Oldfusiondesigns/OFD_Flycore_Straight_Talon/Images/Capture.PNG

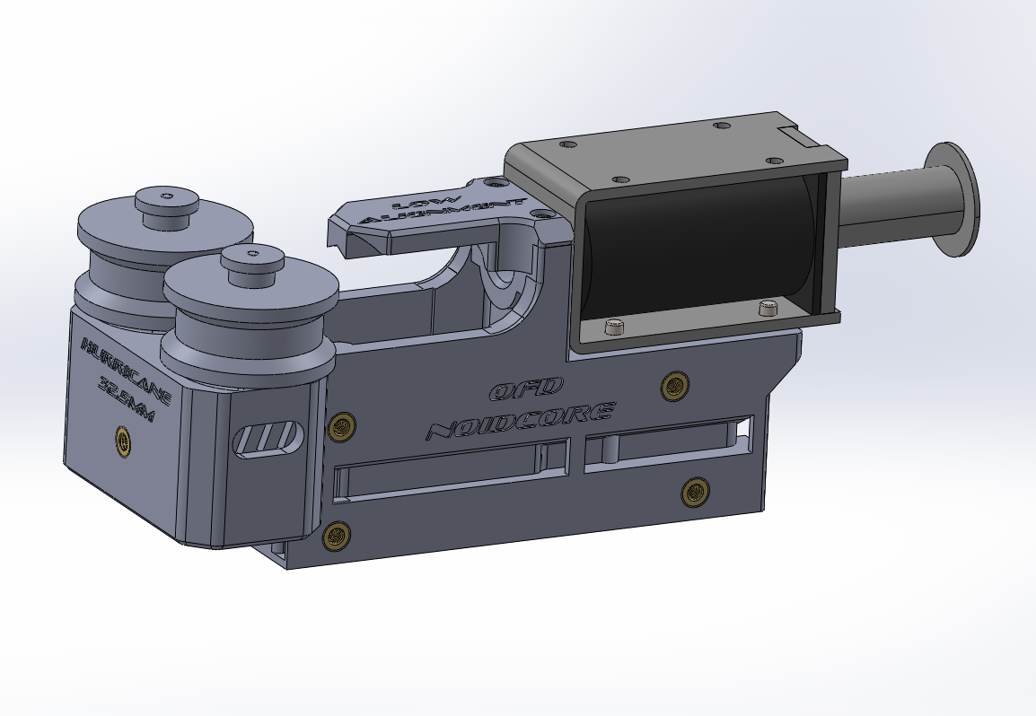
Images/Capture.PNG
