Oldfusiondesigns/OFD_Flycore_Straight_Talon/Images/heatsets.jpg

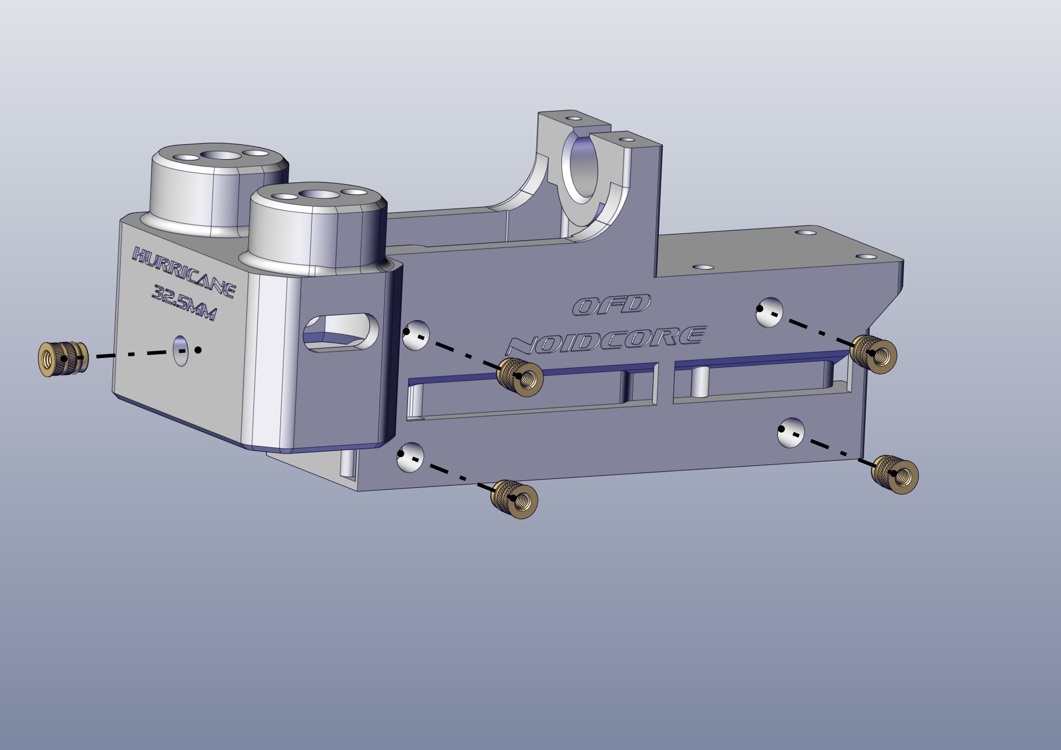
Images/heatsets.jpg
