Oldfusiondesigns/OFD_Flycore_Straight_Talon/Flycore Straight Talon/STLs/Flywheel_Spacers/OFD_Flywheel_Spacer_3.5mm_V1.STL

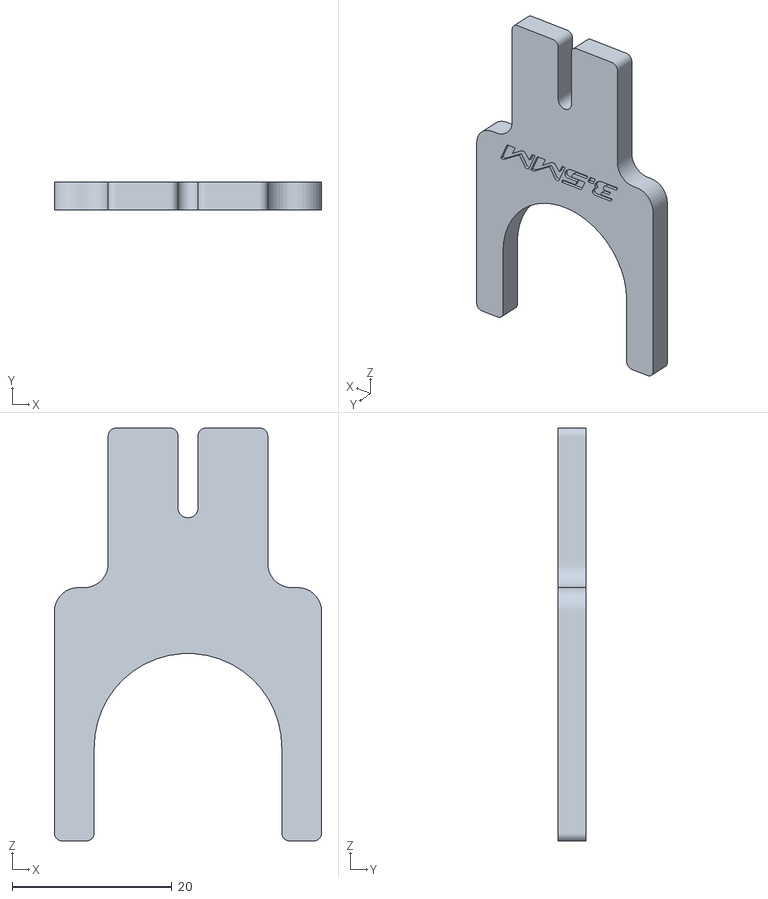
[picture p27: CAD file, 2022-10-01]
Flycore Straight Talon/STLs/Flywheel_Spacers/OFD_Flywheel_Spacer_3.5mm_V1.STL
33.5 x 3.50 x 51.8
