Oldfusiondesigns/OFD_Flycore_Straight_Talon/Flycore Straight Talon/STEPs/Pusher_Wheel_Plus_.4_V1.STEP

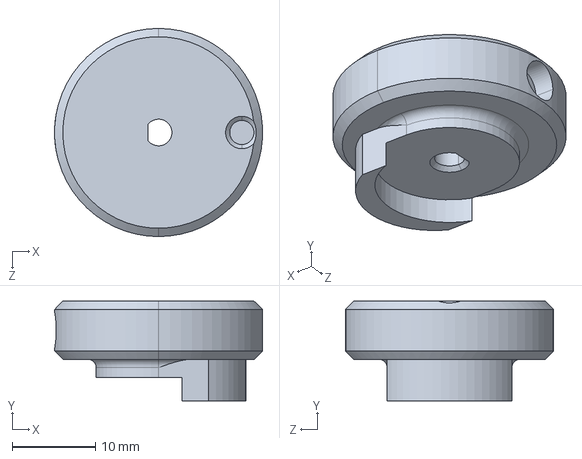
[picture p28: CAD file, 2022-10-01]
Flycore Straight Talon/STEPs/Pusher_Wheel_Plus_.4_V1.STEP
25.0 x 12.0 x 25.0 mm
