Oldfusiondesigns/OFD_Flycore_Straight_Talon/Flycore Straight Talon/STLs/Flywheel_Spacers/OFD_Flywheel_Spacer_2mm_V1.STL

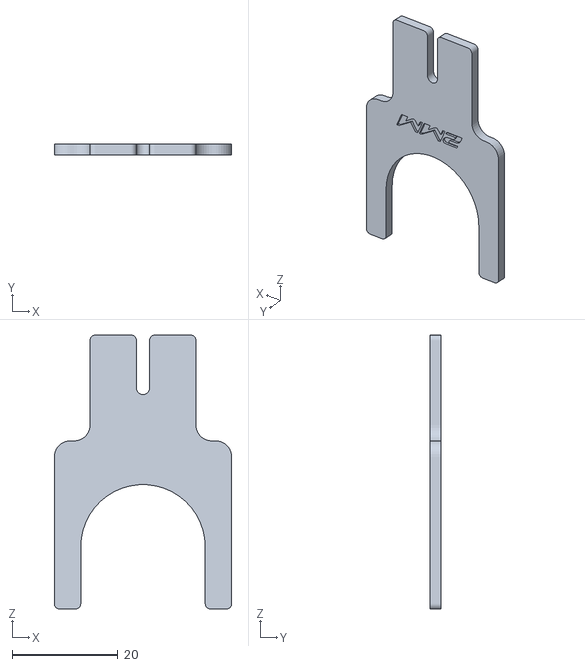
[picture p29: CAD file, 2022-10-01]
Flycore Straight Talon/STLs/Flywheel_Spacers/OFD_Flywheel_Spacer_2mm_V1.STL
33.5 x 2.00 x 51.8
