Oldfusiondesigns/OFD_Flycore_Straight_Talon/Flycore Straight Talon/STLs/Flywheel_Spacers/OFD_Flywheel_Spacer_1mm_V1.STL

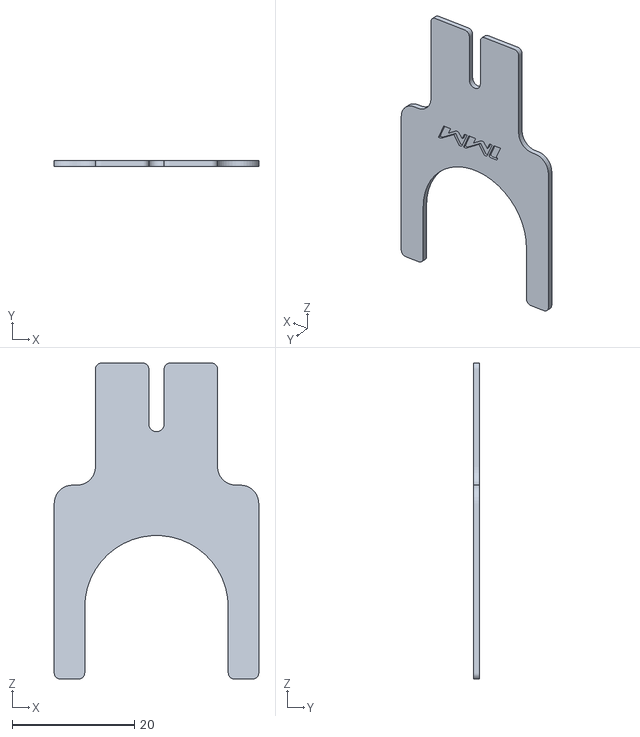
[picture p30: CAD file, 2022-10-01]
Flycore Straight Talon/STLs/Flywheel_Spacers/OFD_Flywheel_Spacer_1mm_V1.STL
33.5 x 1.00 x 51.8
