Oldfusiondesigns/OFD_Flycore_Straight_Talon/Flycore Straight Talon/STEPs/Pusher_Guide_Straight_V1.STEP

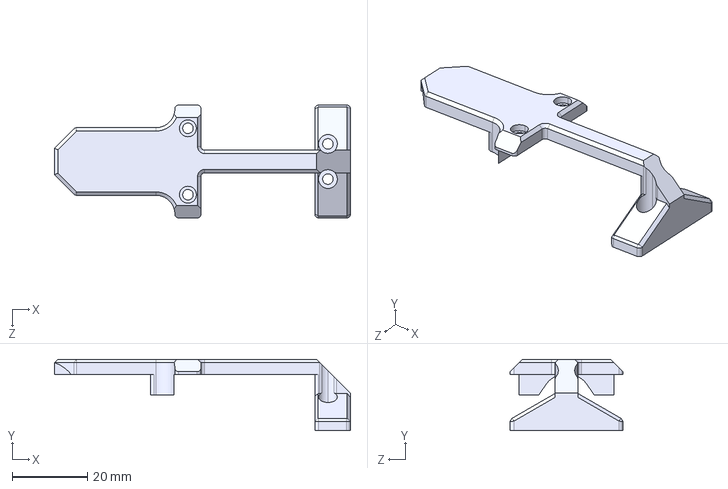
[picture p31: CAD file, 2022-10-01]
Flycore Straight Talon/STEPs/Pusher_Guide_Straight_V1.STEP
78.7 x 19.0 x 30.0 mm
