Oldfusiondesigns/OFD_Flycore_Straight_Talon/Flycore Straight Talon/STEPs/Straight_Mag_Detent_V1.STEP

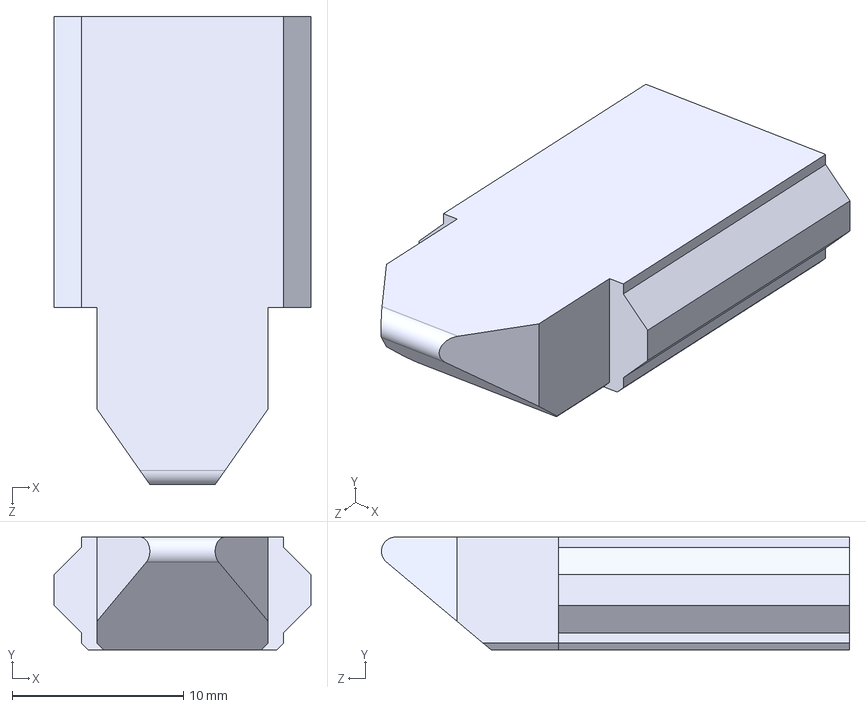
[picture p32: CAD file, 2022-10-01]
Flycore Straight Talon/STEPs/Straight_Mag_Detent_V1.STEP
15.0 x 6.60 x 27.4 mm
