Oldfusiondesigns/OFD_Flycore_Straight_Talon/Flycore Straight Talon/STEPs/Straight_Mag_Release_V1.STEP

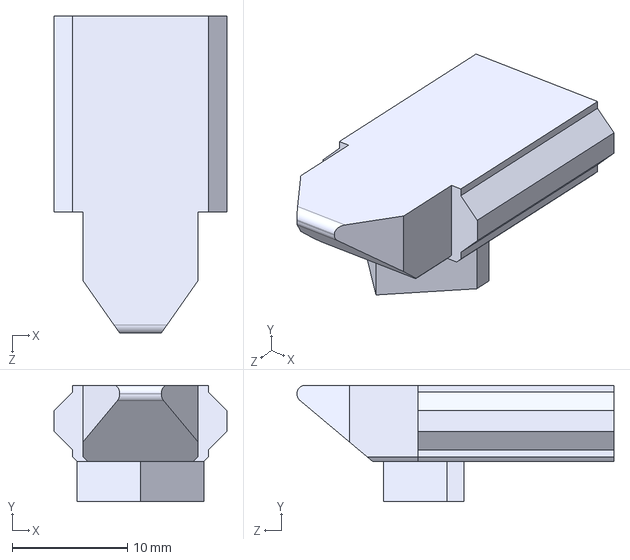
[picture p33: CAD file, 2022-10-01]
Flycore Straight Talon/STEPs/Straight_Mag_Release_V1.STEP
15.0 x 10.1 x 27.5 mm
