Oldfusiondesigns/OFD_Flycore_Straight_Talon/Flycore Straight Talon/STEPs/Pusher_V1.STEP

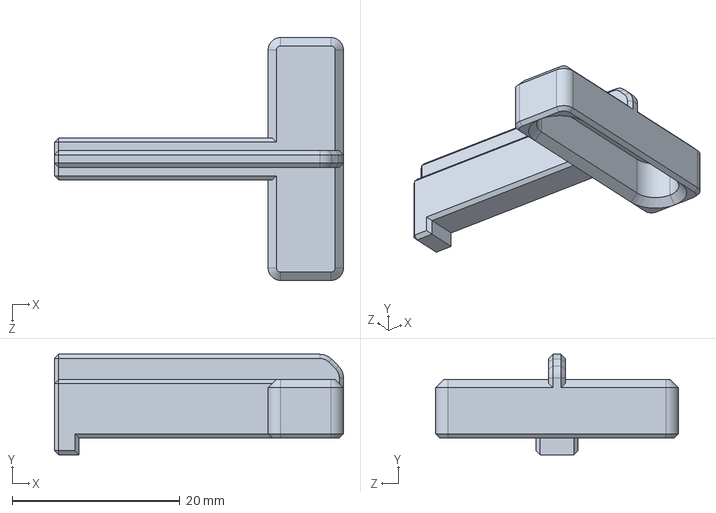
[picture p34: CAD file, 2022-10-01]
Flycore Straight Talon/STEPs/Pusher_V1.STEP
34.5 x 12.0 x 29.0 mm
